rgronberg/fireplace-315mhz/circuit/fireplace.kicad_sch

## KiCad design circuit/fireplace.kicad_sch (2024-11-23)

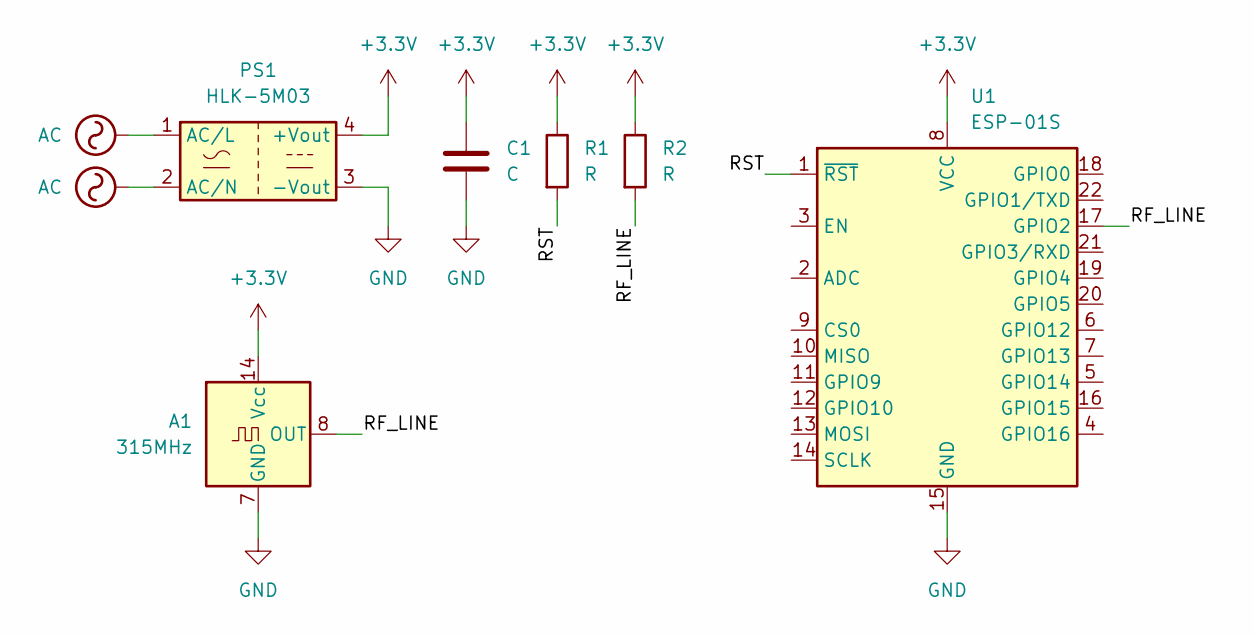
[picture p4: schematic fireplace.kicad_sch]

Parts:
A1: 315MHz
C1: C
PS1: HLK-5M03; Converter_ACDC_Hi-Link_HLK-5Mxx
R1, R2: R
U1: ESP-01S; ESP-12E

Connections:
+3.3V: A1.14 (Vcc), C1.1, PS1.4 (+Vout), R1.1, R2.1, U1.8 (VCC)
AC: PS1.1 (AC/L), PS1.2 (AC/N)
GND: A1.7 (GND), C1.2, PS1.3 (-Vout), U1.15 (GND)
RF_LINE: A1.8 (OUT), R2.2, U1.17 (GPIO2)
RST: R1.2, U1.1 (~RST)
